myriadrf/Novena-RF/hardware/v1/VIA_OFF_PAD_v.1_r.10/KiCAD/Clocks, RF FE.sch

## KiCad design hardware/v1/VIA_OFF_PAD_v.1_r.10/KiCAD/Clocks, RF FE.sch (2014-10-09)

Schematic: Clocks, RF FE.sch

Parts:
C12, C28, C30, C32, C74, C75, C76, C84, C85: 100nF; C_SM0402; Manufacturer Part Number C0402C104K8PACTU
C26, C77: 100pF; C_SM0402; Manufacturer Part Number GRM1555C1H101JD01D
C29: 1nF; C_SM0402; Manufacturer Part Number CC0402KRX7R9BB102
DA4: CDCV304PW; TSSOP-8; Manufacturer Part Number CDCV304PWR
DA5: PE42440; QFN-16; Manufacturer Part Number PE42440
DA6: PE42422; QFN12; Manufacturer Part Number PE42422MLAA-Z
R2, R3, R50: 1M; R_SM0402; Manufacturer Part Number RC0402FR-071ML
R4, R25, R26, R27, R28, R29, R49: 0; R_SM0402; Manufacturer Part Number RC0402JR-070RL
R69: 49.9; R_SM0402; Manufacturer Part Number MC 0.0625W 0402 1% 49R9
RT1: POT; RT_SMD; Manufacturer Part Number 43WR10KLFTR
X6, X7: U.FL; Manufacturer Part Number 0734120110
XO1: RACON_TXCO_NF; SMD_TXCO; Manufacturer Part Number E5280LF
XO2: RTX5032A_30.72MHZ; SMD_RTX5032A; Manufacturer Part Number 509464

Notes on the sheet:
TX TEST
RX TEST
