myriadrf/Novena-RF/hardware/v1/VIA_OFF_PAD_v.1_r.10/KiCAD/Connectors.sch

## KiCad design hardware/v1/VIA_OFF_PAD_v.1_r.10/KiCAD/Connectors.sch (2014-10-09)

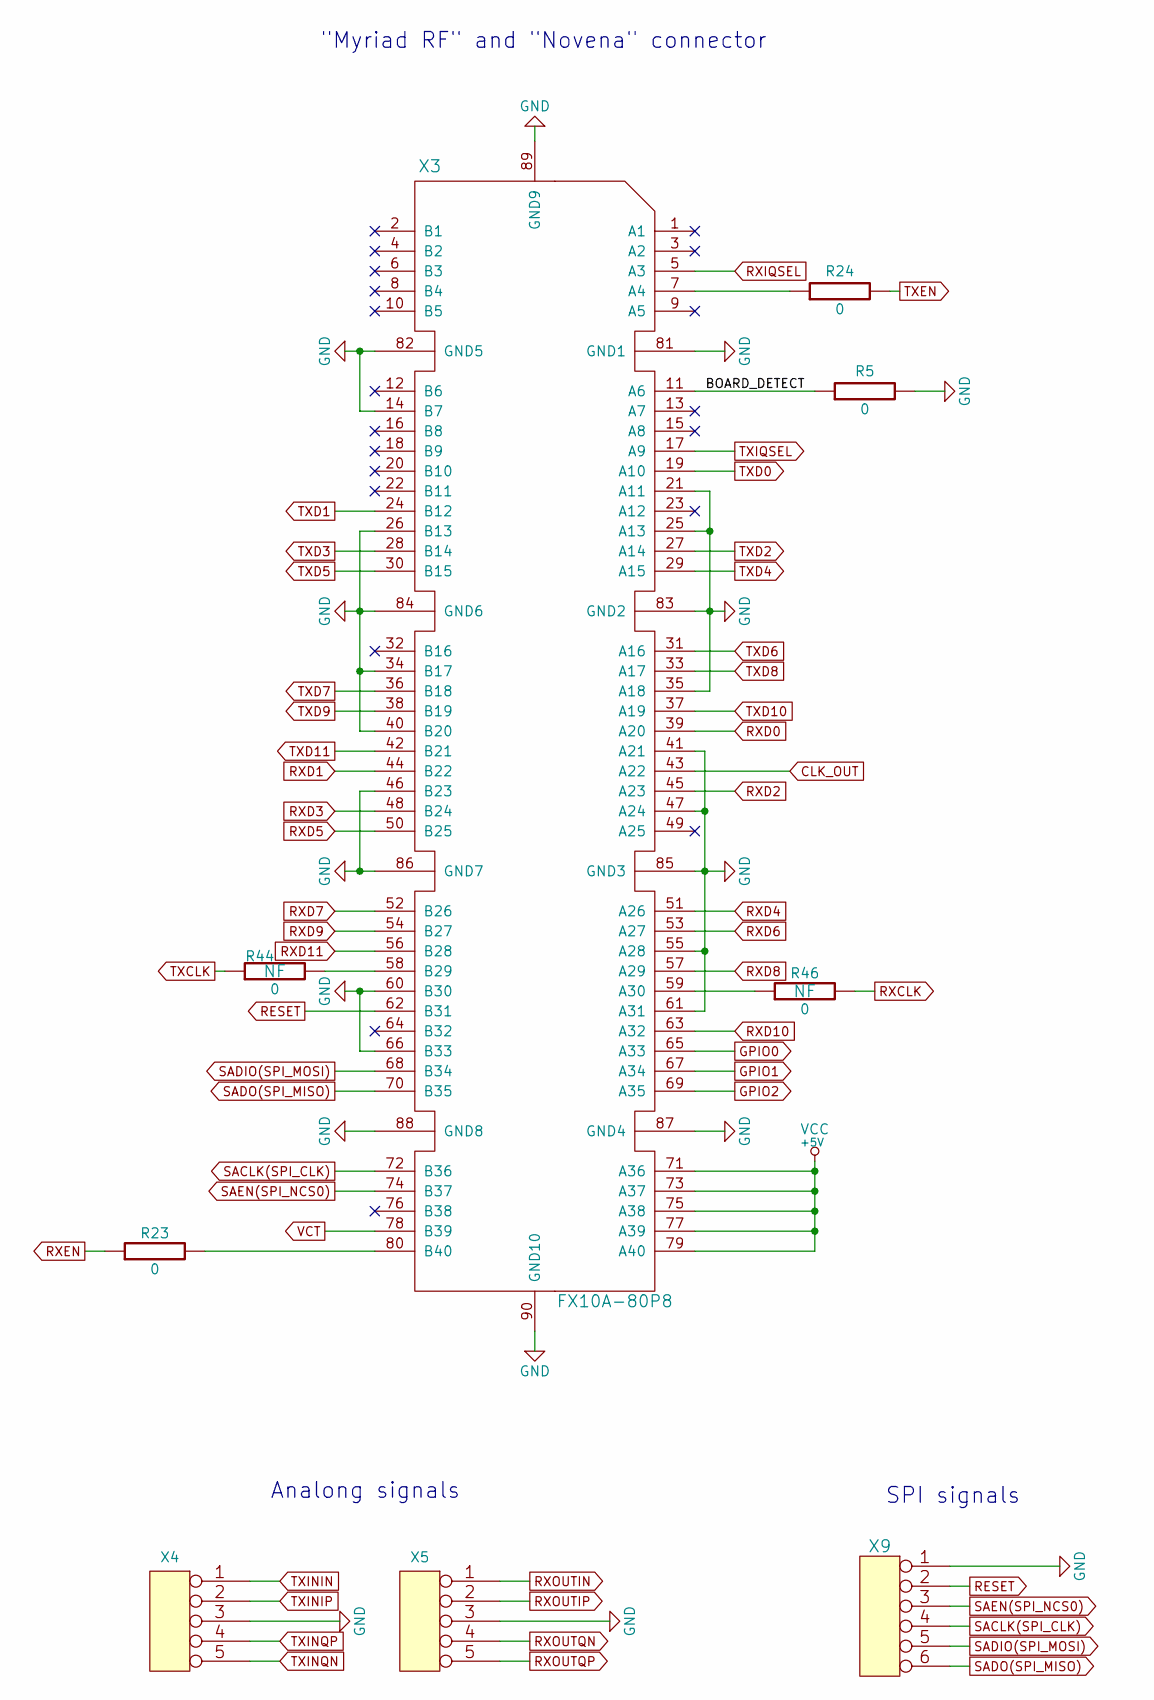
[picture p41: schematic Connectors.sch]

Parts:
R5, R23, R24, R44, R46: 0; R_SM0402; Manufacturer Part Number RC0402JR-070RL
X3: FX10A-80P8; Manufacturer Part Number FX10B-80P/8-SV1(71)
X4, X5: 5-104348-3; VR_pinhead5; Manufacturer Part Number 5-104348-3
X9: CONN_6; pinhead6; Manufacturer Part Number 104345-4

Connections:
BOARD_DETECT: R5.1, X3.11 (A6)
CLK_OUT: X3.43 (A22)
GND: R5.2, X3.14 (B7), X3.21 (A11), X3.25 (A13), X3.26 (B13), X3.34 (B17), X3.35 (A18), X3.40 (B20), X3.41 (A21), X3.46 (B23), X3.47 (A24), X3.55 (A28), X3.60 (B30), X3.61 (A31), X3.66 (B33), X3.81 (GND1), X3.82 (GND5), X3.83 (GND2), X3.84 (GND6), X3.85 (GND3), X3.86 (GND7), X3.87 (GND4), X3.88 (GND8), X3.89 (GND9), X3.90 (GND10), X4.3, X5.3, X9.1
GPIO0: X3.65 (A33)
GPIO1: X3.67 (A34)
GPIO2: X3.69 (A35)
unnamed: R23.2, X3.80 (B40)
unnamed: R24.1, X3.7 (A4)
unnamed: R44.2, X3.58 (B29)
unnamed: R46.1, X3.59 (A30)
RESET: X3.62 (B31), X9.2
RXCLK: R46.2
RXD0: X3.39 (A20)
RXD1: X3.44 (B22)
RXD2: X3.45 (A23)
RXD3: X3.48 (B24)
RXD4: X3.51 (A26)
RXD5: X3.50 (B25)
RXD6: X3.53 (A27)
RXD7: X3.52 (B26)
RXD8: X3.57 (A29)
RXD9: X3.54 (B27)
RXD10: X3.63 (A32)
RXD11: X3.56 (B28)
RXEN: R23.1
RXIQSEL: X3.5 (A3)
RXOUTIN: X5.1
RXOUTIP: X5.2
RXOUTQN: X5.4
RXOUTQP: X5.5
SACLK(SPI_CLK): X3.72 (B36), X9.4
SADIO(SPI_MOSI): X3.68 (B34), X9.5
SADO(SPI_MISO): X3.70 (B35), X9.6
SAEN(SPI_NCS0): X3.74 (B37), X9.3
TXCLK: R44.1
TXD0: X3.19 (A10)
TXD1: X3.24 (B12)
TXD2: X3.27 (A14)
TXD3: X3.28 (B14)
TXD4: X3.29 (A15)
TXD5: X3.30 (B15)
TXD6: X3.31 (A16)
TXD7: X3.36 (B18)
TXD8: X3.33 (A17)
TXD9: X3.38 (B19)
TXD10: X3.37 (A19)
TXD11: X3.42 (B21)
TXEN: R24.2
TXININ: X4.1
TXINIP: X4.2
TXINQN: X4.5
TXINQP: X4.4
TXIQSEL: X3.17 (A9)
VCC: X3.71 (A36), X3.73 (A37), X3.75 (A38), X3.77 (A39), X3.79 (A40)
VCT: X3.78 (B39)

Notes on the sheet:
"Myriad RF" and "Novena" connector
Analong signals
SPI signals
