myriadrf/Novena-RF/hardware/v1/VIA_OFF_PAD_v.1_r.10/KiCAD/Digital Circuits.sch

## KiCad design hardware/v1/VIA_OFF_PAD_v.1_r.10/KiCAD/Digital Circuits.sch (2014-10-09)

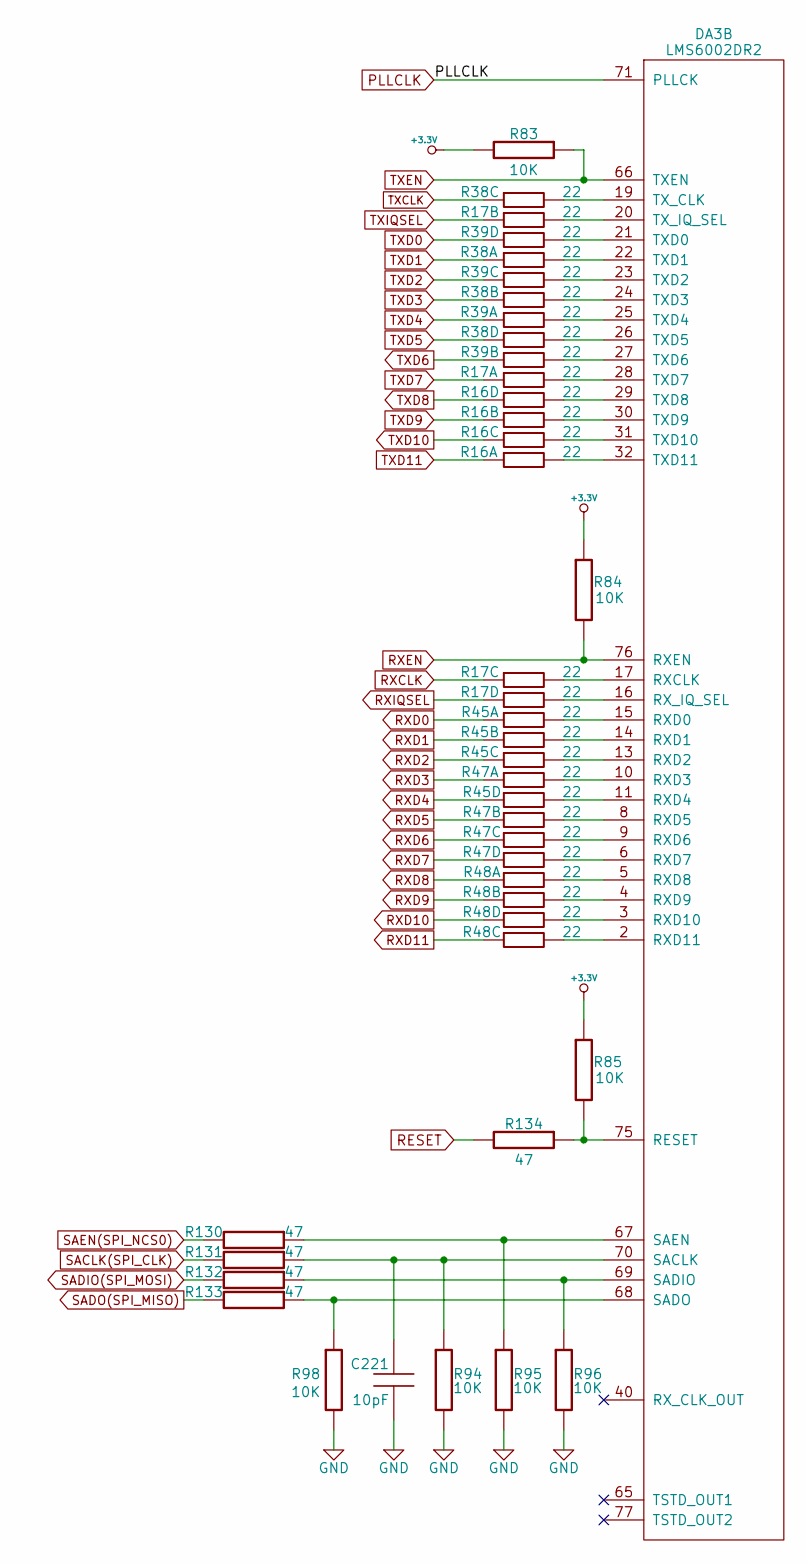
[picture p42: schematic Digital Circuits.sch]

Parts:
C221: 10pF; C_SM0402; Manufacturer Part Number MC0402N100F500CT
DA3: LMS6002DR2; LMS6002; Manufacturer Part Number LMS6002DR2
R16, R17, R38, R39, R45, R47, R48: 22
R83, R84, R85, R94, R95, R96, R98: 10K; R_SM0402; Manufacturer Part Number RC0402FR-1310KL
R130, R131, R132, R133, R134: 47; R_SM0402; Manufacturer Part Number RC0402FR-0747RL

Connections:
+3.3V: R83.2, R84.1, R85.1
GND: C221.2, R94.2, R95.2, R96.2, R98.2
unnamed: C221.1, DA3.70 (SACLK), R94.1, R131.1
unnamed: DA3.2 (RXD11), R48.6
unnamed: DA3.3 (RXD10), R48.5
unnamed: DA3.4 (RXD9), R48.7
unnamed: DA3.5 (RXD8), R48.8
unnamed: DA3.6 (RXD7), R47.5
unnamed: DA3.8 (RXD5), R47.7
unnamed: DA3.9 (RXD6), R47.6
unnamed: DA3.10 (RXD3), R47.8
unnamed: DA3.11 (RXD4), R45.5
unnamed: DA3.13 (RXD2), R45.6
unnamed: DA3.14 (RXD1), R45.7
unnamed: DA3.15 (RXD0), R45.8
unnamed: DA3.16 (RX_IQ_SEL), R17.5
unnamed: DA3.17 (RXCLK), R17.6
unnamed: DA3.19 (TX_CLK), R38.6
unnamed: DA3.20 (TX_IQ_SEL), R17.7
unnamed: DA3.21 (TXD0), R39.5
unnamed: DA3.22 (TXD1), R38.8
unnamed: DA3.23 (TXD2), R39.6
unnamed: DA3.24 (TXD3), R38.7
unnamed: DA3.25 (TXD4), R39.8
unnamed: DA3.26 (TXD5), R38.5
unnamed: DA3.27 (TXD6), R39.7
unnamed: DA3.28 (TXD7), R17.8
unnamed: DA3.29 (TXD8), R16.5
unnamed: DA3.30 (TXD9), R16.7
unnamed: DA3.31 (TXD10), R16.6
unnamed: DA3.32 (TXD11), R16.8
unnamed: DA3.67 (SAEN), R95.1, R130.1
unnamed: DA3.68 (SADO), R98.1, R133.1
unnamed: DA3.69 (SADIO), R96.1, R132.1
unnamed: DA3.75 (RESET), R85.2, R134.1
PLLCLK: DA3.71 (PLLCK)
RESET: R134.2
RXCLK: R17.3
RXD0: R45.1
RXD1: R45.2
RXD2: R45.3
RXD3: R47.1
RXD4: R45.4
RXD5: R47.2
RXD6: R47.3
RXD7: R47.4
RXD8: R48.1
RXD9: R48.2
RXD10: R48.4
RXD11: R48.3
RXEN: DA3.76 (RXEN), R84.2
RXIQSEL: R17.4
SACLK(SPI_CLK): R131.2
SADIO(SPI_MOSI): R132.2
SADO(SPI_MISO): R133.2
SAEN(SPI_NCS0): R130.2
TXCLK: R38.3
TXD0: R39.4
TXD1: R38.1
TXD2: R39.3
TXD3: R38.2
TXD4: R39.1
TXD5: R38.4
TXD6: R39.2
TXD7: R17.1
TXD8: R16.4
TXD9: R16.2
TXD10: R16.3
TXD11: R16.1
TXEN: DA3.66 (TXEN), R83.1
TXIQSEL: R17.2
