myriadrf/Novena-RF/driver/fpga/bclk_dll/bclk_dll.vhd

-- file: bclk_dll.vhd
-- 
-- (c) Copyright 2008 - 2011 Xilinx, Inc. All rights reserved.
-- 
-- This file contains confidential and proprietary information
-- of Xilinx, Inc. and is protected under U.S. and
-- international copyright and other intellectual property
-- laws.
-- 
-- DISCLAIMER
-- This disclaimer is not a license and does not grant any
-- rights to the materials distributed herewith. Except as
-- otherwise provided in a valid license issued to you by
-- Xilinx, and to the maximum extent permitted by applicable
-- law: (1) THESE MATERIALS ARE MADE AVAILABLE "AS IS" AND
-- WITH ALL FAULTS, AND XILINX HEREBY DISCLAIMS ALL WARRANTIES
-- AND CONDITIONS, EXPRESS, IMPLIED, OR STATUTORY, INCLUDING
-- BUT NOT LIMITED TO WARRANTIES OF MERCHANTABILITY, NON-
-- INFRINGEMENT, OR FITNESS FOR ANY PARTICULAR PURPOSE; and
-- (2) Xilinx shall not be liable (whether in contract or tort,
-- including negligence, or under any other theory of
-- liability) for any loss or damage of any kind or nature
-- related to, arising under or in connection with these
-- materials, including for any direct, or any indirect,
-- special, incidental, or consequential loss or damage
-- (including loss of data, profits, goodwill, or any type of
-- loss or damage suffered as a result of any action brought
-- by a third party) even if such damage or loss was
-- reasonably foreseeable or Xilinx had been advised of the
-- possibility of the same.
-- 
-- CRITICAL APPLICATIONS
-- Xilinx products are not designed or intended to be fail-
-- safe, or for use in any application requiring fail-safe
-- performance, such as life-support or safety devices or
-- systems, Class III medical devices, nuclear facilities,
-- applications related to the deployment of airbags, or any
-- other applications that could lead to death, personal
-- injury, or severe property or environmental damage
-- (individually and collectively, "Critical
-- Applications"). Customer assumes the sole risk and
-- liability of any use of Xilinx products in Critical
-- Applications, subject only to applicable laws and
-- regulations governing limitations on product liability.
-- 
-- THIS COPYRIGHT NOTICE AND DISCLAIMER MUST BE RETAINED AS
-- PART OF THIS FILE AT ALL TIMES.
-- 
------------------------------------------------------------------------------
-- User entered comments
------------------------------------------------------------------------------
-- None
--
------------------------------------------------------------------------------
-- "Output    Output      Phase     Duty      Pk-to-Pk        Phase"
-- "Clock    Freq (MHz) (degrees) Cycle (%) Jitter (ps)  Error (ps)"
------------------------------------------------------------------------------
-- CLK_OUT1___133.014______0.000______50.0______200.000____150.000
--
------------------------------------------------------------------------------
-- "Input Clock   Freq (MHz)    Input Jitter (UI)"
------------------------------------------------------------------------------
-- __primary_________133.014_____________0.01

library ieee;
use ieee.std_logic_1164.all;
use ieee.std_logic_unsigned.all;
use ieee.std_logic_arith.all;
use ieee.numeric_std.all;

library unisim;
use unisim.vcomponents.all;

entity bclk_dll is
port
 (-- Clock in ports
  clk133in           : in     std_logic;
  -- Clock out ports
  clk133          : out    std_logic;
  -- Status and control signals
  RESET             : in     std_logic;
  LOCKED            : out    std_logic
 );
end bclk_dll;

architecture xilinx of bclk_dll is
  attribute CORE_GENERATION_INFO : string;
  attribute CORE_GENERATION_INFO of xilinx : architecture is "bclk_dll,clk_wiz_v4_1,{component_name=bclk_dll,use_phase_alignment=true,use_min_o_jitter=false,use_max_i_jitter=false,use_dyn_phase_shift=false,use_inclk_switchover=false,use_dyn_reconfig=false,feedback_source=FDBK_AUTO,primtype_sel=DCM_SP,num_out_clk=1,clkin1_period=7.518,clkin2_period=7.518,use_power_down=false,use_reset=true,use_locked=true,use_inclk_stopped=false,use_status=false,use_freeze=false,use_clk_valid=false,feedback_type=SINGLE,clock_mgr_type=AUTO,manual_override=false}";
	  -- Input clock buffering / unused connectors
  signal clkin1            : std_logic;
  -- Output clock buffering
  signal clk_out1_internal : std_logic;
  signal clkfb             : std_logic;
  signal clk0              : std_logic;
  signal clkfbout          : std_logic;
  signal locked_internal   : std_logic;
  signal status_internal   : std_logic_vector(7 downto 0);
begin


  -- Input buffering
  --------------------------------------
  clkin1 <= clk133in;


  -- Clocking primitive
  --------------------------------------
  
  -- Instantiation of the DCM primitive
  --    * Unused inputs are tied off
  --    * Unused outputs are labeled unused
  dcm_sp_inst: DCM_SP
  generic map
   (CLKDV_DIVIDE          => 2.000,
    CLKFX_DIVIDE          => 1,
    CLKFX_MULTIPLY        => 4,
    CLKIN_DIVIDE_BY_2     => FALSE,
    CLKIN_PERIOD          => 7.518,
    CLKOUT_PHASE_SHIFT    => "NONE",
    CLK_FEEDBACK          => "1X",
    DESKEW_ADJUST         => "SYSTEM_SYNCHRONOUS",
    PHASE_SHIFT           => 0,
    STARTUP_WAIT          => FALSE)
  port map
   -- Input clock
   (CLKIN                 => clkin1,
    CLKFB                 => clkfb,
    -- Output clocks
    CLK0                  => clk0,
    CLK90                 => open,
    CLK180                => open,
    CLK270                => open,
    CLK2X                 => open,
    CLK2X180              => open,
    CLKFX                 => open,
    CLKFX180              => open,
    CLKDV                 => open,
   -- Ports for dynamic phase shift
    PSCLK                 => '0',
    PSEN                  => '0',
    PSINCDEC              => '0',
    PSDONE                => open,
   -- Other control and status signals
    LOCKED                => locked_internal,
    STATUS                => status_internal,
    RST                   => RESET,
   -- Unused pin, tie low
    DSSEN                 => '0');

  LOCKED                <= locked_internal;



  -- Output buffering
  -------------------------------------
  clkfb <= clk_out1_internal;


  clkout1_buf : BUFG
  port map
   (O   => clk_out1_internal,
    I   => clk0);


  clk133 <= clk_out1_internal;

end xilinx;
