myriadrf/Novena-RF/driver/host/NovenaLMS6.cpp

////////////////////////////////////////////////////////////////////////
// SoapySDR module for Novena-RF SDR
//
// Copyright (c) 2015-2015 Lime Microsystems
// Copyright (c) 2015-2015 Andrew "bunnie" Huang
// SPDX-License-Identifier: Apache-2.0
// http://www.apache.org/licenses/LICENSE-2.0
////////////////////////////////////////////////////////////////////////

#include "NovenaRF.hpp"
#include "LMS6002_MainControl.h"
#include "lms6/CompoundOperations.h"
#include "lms6/Algorithms.h"
#include "MessageLog.h"

#include <sys/stat.h>
#include <pthread.h>
#include <fstream>

/***********************************************************************
 * Log handler from the lms suite
 **********************************************************************/
class SignalHandlerLogger : public SignalHandler
{
public:
    SignalHandlerLogger(void)
    {
        return;
    }

    void HandleMessage(const LMS_Message &msg)
    {
        switch (msg.type)
        {
        case MSG_ERROR: SoapySDR::log(SOAPY_SDR_ERROR, msg.text); break;
        case MSG_WARNING: SoapySDR::log(SOAPY_SDR_WARNING, msg.text); break;
        default: SoapySDR::log(SOAPY_SDR_INFO, msg.text); break;
        }
    }
};

static SignalHandlerLogger myLogger;

/***********************************************************************
 * handler for interfacing with LMS6 registers from unix fifo
 **********************************************************************/
#define NOVENA_RF_CMD_PATH "/tmp/novena_rf_cmd"
#define NOVENA_RF_OUT_PATH "/tmp/novena_rf_out"
static pthread_t fifoAccessThread;

void *fifoAccessHandler(void *arg)
{
    auto regMap = reinterpret_cast<lms6::RegistersMap *>(arg);

    mkfifo(NOVENA_RF_CMD_PATH, S_IWUSR | S_IRUSR);
    mkfifo(NOVENA_RF_OUT_PATH, S_IWUSR | S_IRUSR);

    while (true)
    {
        //read cmd fifo
        std::ifstream cmdFile(NOVENA_RF_CMD_PATH);
        std::string line;
        std::getline(cmdFile, line);
        if (line.empty()) continue;
        if (line == "exit") break;

        //parse command
        std::string adrStr, valStr;
        std::stringstream ss(line);
        std::getline(ss, adrStr, ' ');
        std::getline(ss, valStr, ' ');
        const long adr = (adrStr.substr(0, 2) == "0x")?strtol(adrStr.c_str(), nullptr, 16):strtol(adrStr.c_str(), nullptr, 10);
        const long val = (valStr.substr(0, 2) == "0x")?strtol(valStr.c_str(), nullptr, 16):strtol(valStr.c_str(), nullptr, 10);

        //perform write it value specified
        if (not valStr.empty()) regMap->SetRegisterValue(adr, val);

        //perform a read and output to the result
        const int out = regMap->GetRegisterValue(adr, true/*from chip*/);
        std::ofstream outFile(NOVENA_RF_OUT_PATH);
        outFile << std::hex << "0x" << out << std::endl;
    }

    return nullptr;
}

/***********************************************************************
 * Setup and tear-down hooks
 * Initialize everything on the lms6 for runtime usage.
 * Configurable parameters are in the sections below.
 **********************************************************************/
void NovenaRF::initRFIC(void)
{
    _calLPFCoreOnce = 0;

    auto ser = new ConnectionManager();
    ser->RegisterForNotifications(&myLogger);
    ser->Open();

    //separate logger - enable to console
    //MessageLog::getInstance()->SetConsoleFilter(LOG_ALL, true);

    //main control owns the connection manager
    _lms6ctrl = new lms6::LMS6002_MainControl(ser);
    _lms6ctrl->ResetChip(LMS_RST_PULSE);
    _lms6ctrl->NewProject();
    SoapySDR::logf(SOAPY_SDR_INFO, "LMS6002: ver=0x%x, rev=0x%x",
        _lms6ctrl->GetParam(lms6::VER), _lms6ctrl->GetParam(lms6::REV));

    _lms6ctrl->SetReferenceFrequency(this->getMasterClockRate()/1e6, true/*Rx*/);
    _lms6ctrl->SetReferenceFrequency(this->getMasterClockRate()/1e6, false/*Tx*/);

    _lms6ctrl->SetParam(lms6::STXEN, 1); //enable transmitter
    _lms6ctrl->SetParam(lms6::SRXEN, 1); //enable receiver

    //enable all the things
    _lms6ctrl->SetParam(lms6::EN_TOP, 1);
    _lms6ctrl->SetParam(lms6::EN_RXPLL, 1);
    _lms6ctrl->SetParam(lms6::EN_TXPLL, 1);
    _lms6ctrl->SetParam(lms6::EN_ADC_DAC, 1);
    _lms6ctrl->SetParam(lms6::EN_TXRF, 1);
    _lms6ctrl->SetParam(lms6::EN_RXFE, 1);
    _lms6ctrl->SetParam(lms6::EN_RXLPF, 1);
    _lms6ctrl->SetParam(lms6::EN_TXLPF, 1);
    _lms6ctrl->SetParam(lms6::EN_RXVGA2, 1);
    lms6::CompoundOperations(_lms6ctrl).CustSet_RxVGA2PowerON();
    lms6::CompoundOperations(_lms6ctrl).CustSet_LNAPowerON();
    lms6::CompoundOperations(_lms6ctrl).CustSet_RxLpfPowerON();
    lms6::CompoundOperations(_lms6ctrl).CustSet_RxFePowerON();

    //bypass LPF by default with large BW
    this->setBandwidth(SOAPY_SDR_TX, 0, 30.0e6);
    this->setBandwidth(SOAPY_SDR_RX, 0, 30.0e6);

    //initialize to minimal gain settings
    SoapySDR::Device::setGain(SOAPY_SDR_TX, 0, 0.0);
    SoapySDR::Device::setGain(SOAPY_SDR_RX, 0, 0.0);

    //initialize antenna to broadband
    this->setAntenna(SOAPY_SDR_TX, 0, "BB");
    this->setAntenna(SOAPY_SDR_RX, 0, "BB");

    //set expected interface mode
    _lms6ctrl->SetParam(lms6::MISC_CTRL_9, 0); //rx fsync polarity
    _lms6ctrl->SetParam(lms6::MISC_CTRL_8, 1); //rx interleave mode (swap for std::complex host format)
    _lms6ctrl->SetParam(lms6::MISC_CTRL_6, 1); //tx fsync polarity (tx needs this swap for an unknown reason)
    _lms6ctrl->SetParam(lms6::MISC_CTRL_5, 1); //tx interleave mode (swap for std::complex host format)

    //start the register handler thread
    if (pthread_create(&fifoAccessThread, nullptr, fifoAccessHandler, _lms6ctrl->getRegistersMap()) != 0)
    {
        SoapySDR::log(SOAPY_SDR_ERROR, "Error creating fifo access thread");
    }
}

void NovenaRF::exitRFIC(void)
{
    //stop the register handler thread
    std::ofstream cmdFile(NOVENA_RF_CMD_PATH);
    cmdFile << "exit" << std::endl;
    cmdFile.close();
    pthread_join(fifoAccessThread, nullptr);

    //_lms6ctrl->SaveToFile("/tmp/lms6.txt", false);
    _lms6ctrl->SetParam(lms6::STXEN, 0); //disable transmitter
    _lms6ctrl->SetParam(lms6::SRXEN, 0); //disable receiver
    lms6::CompoundOperations(_lms6ctrl).CustSet_RxVGA2PowerOFF();
    lms6::CompoundOperations(_lms6ctrl).CustSet_LNAPowerOFF();
    lms6::CompoundOperations(_lms6ctrl).CustSet_RxLpfPowerOFF();
    lms6::CompoundOperations(_lms6ctrl).CustSet_RxFePowerOFF();

    delete _lms6ctrl;
    _lms6ctrl = nullptr;
}

/*******************************************************************
 * Gain API
 *
 * Available amplification/attenuation elements are listed in order
 * from RF to BB for the default gain distribution algorithm.
 *
 * Gains are passed in as dB and clipped and scaled into integer values
 * for the specific registers to which they apply.
 ******************************************************************/
std::vector<std::string> NovenaRF::listGains(const int direction, const size_t channel) const
{
    std::vector<std::string> gains;
    if (direction == SOAPY_SDR_TX)
    {
        //ordering RF to BB
        gains.push_back("VGA2");
        gains.push_back("VGA1");
    }
    if (direction == SOAPY_SDR_RX)
    {
        //ordering RF to BB
        gains.push_back("LNA");
        gains.push_back("VGA1");
        gains.push_back("VGA2");
    }
    return gains;
}

#define MinMaxClip(minimum, maximum, value) \
    std::max(minimum, std::min(maximum, value))

void NovenaRF::setGain(const int direction, const size_t channel, const std::string &name, const double value)
{
    if (direction == SOAPY_SDR_TX and name == "VGA1")
    {
        const double regVal(MinMaxClip(-35.0, -4.0, value));
        _lms6ctrl->SetParam(lms6::VGA1GAIN, lrint(regVal+35.0));
    }
    if (direction == SOAPY_SDR_TX and name == "VGA2")
    {
        const double regVal(MinMaxClip(0.0, 25.0, value));
        _lms6ctrl->SetParam(lms6::VGA2GAIN_TXVGA2, lrint(regVal));
    }
    if (direction == SOAPY_SDR_RX and name == "VGA2")
    {
        const double regVal(MinMaxClip(0.0, 30.0, value));
        _lms6ctrl->SetParam(lms6::VGA2GAIN_RXVGA2, lrint(regVal/3.0));
    }
    if (direction == SOAPY_SDR_RX and name == "VGA1")
    {
        const double regVal(MinMaxClip(0.0, 30.0, value));
        _lms6ctrl->SetParam(lms6::RFB_TIA_RXFE, regVal*4);
    }
    if (direction == SOAPY_SDR_RX and name == "LNA")
    {
        const double regVal(MinMaxClip(0.0, 6.0, value));
        _lms6ctrl->SetParam(lms6::G_LNA_RXFE, 2 | lrint(regVal/6.0));
    }
}

double NovenaRF::getGain(const int direction, const size_t channel, const std::string &name) const
{
    if (direction == SOAPY_SDR_TX and name == "VGA1")
    {
        return _lms6ctrl->GetParam(lms6::VGA1GAIN) - 35.0;
    }
    if (direction == SOAPY_SDR_TX and name == "VGA2")
    {
        return _lms6ctrl->GetParam(lms6::VGA2GAIN_TXVGA2);
    }
    if (direction == SOAPY_SDR_RX and name == "VGA2")
    {
        return _lms6ctrl->GetParam(lms6::VGA2GAIN_RXVGA2)*3.0;
    }
    if (direction == SOAPY_SDR_RX and name == "VGA1")
    {
        return _lms6ctrl->GetParam(lms6::RFB_TIA_RXFE)/4.0;
    }
    if (direction == SOAPY_SDR_RX and name == "LNA")
    {
        return (_lms6ctrl->GetParam(lms6::G_LNA_RXFE) & 0x1)*6.0;
    }
    return SoapySDR::Device::getGain(direction, channel, name);
}

SoapySDR::Range NovenaRF::getGainRange(const int direction, const size_t channel, const std::string &name) const
{
    if (direction == SOAPY_SDR_TX and name == "VGA1") return SoapySDR::Range(-35.0, -4.0);
    if (direction == SOAPY_SDR_TX and name == "VGA2") return SoapySDR::Range(0.0, 25.0);
    if (direction == SOAPY_SDR_RX and name == "VGA2") return SoapySDR::Range(0.0, 30.0);
    if (direction == SOAPY_SDR_RX and name == "VGA1") return SoapySDR::Range(0.0, 30.0);
    if (direction == SOAPY_SDR_RX and name == "LNA") return SoapySDR::Range(0.0, 6.0);
    return SoapySDR::Device::getGainRange(direction, channel, name);
}

/*******************************************************************
 * Frequency API
 *
 * The LO is tuned to the specified frequency in Hz
 * and then the calibration algorithm is applied.
 * Error in tuning the LO is compensated in the CORDIC
 * through the default tuning algorithm.
 ******************************************************************/
void NovenaRF::setRfFrequency(const int direction, const size_t channel, const double frequency, const SoapySDR::Kwargs &)
{
    double realFreq, fVco;
    unsigned Nint, Nfrac, iVco;
    int divider;

    _lms6ctrl->SetFrequency(direction == SOAPY_SDR_RX, frequency/1e6, realFreq, Nint, Nfrac, iVco, fVco, divider);
    _lms6ctrl->Tune(direction == SOAPY_SDR_RX);
    SoapySDR::logf(SOAPY_SDR_TRACE, "NovenaRF: %sTune(%f MHz), actual = %f MHz", (direction==SOAPY_SDR_TX)?"TX":"RX", frequency/1e6, realFreq);
    //SoapySDR::logf(SOAPY_SDR_TRACE, "fVco=%f, Nint=%d, Nfrac=%d, iVco=%d, divider=%d", fVco, Nint, Nfrac, iVco, divider);

    //save gain values
    std::map<std::string, double> save;
    for (const auto &name : this->listGains(direction, channel))
    {
        save[name] = this->getGain(direction, channel, name);
    }

    //apply gain
    if (direction == SOAPY_SDR_RX)
    {
        auto r = SoapySDR::Device::getGainRange(direction, channel);
        SoapySDR::Device::setGain(direction, channel, r.maximum());
    }
    if (direction == SOAPY_SDR_TX)
    {
        this->setGain(direction, channel, "VGA1", -10);
        this->setGain(direction, channel, "VGA2", 25);
    }

    //perform cal with adc off
    _lms6ctrl->SetParam(lms6::EN_ADC_DAC, 0);
    if (_calLPFCoreOnce++ == 0) lms6::Algorithms(_lms6ctrl).CalibrateLPFCore();
    if (direction == SOAPY_SDR_TX) lms6::Algorithms(_lms6ctrl).CalibrateTx();
    if (direction == SOAPY_SDR_RX) lms6::Algorithms(_lms6ctrl).CalibrateRx();
    _lms6ctrl->SetParam(lms6::EN_ADC_DAC, 1);

    //restore gain values
    for (const auto &pair : save)
    {
        this->setGain(direction, channel, pair.first, pair.second);
    }
}

void NovenaRF::setFrequency(const int direction, const size_t channel, const std::string &name, const double frequency, const SoapySDR::Kwargs &args)
{
    //printf("setFrequency %s %f MHz\n", name.c_str(), frequency/1e6);
    if (name == "RF")
    {
        return this->setRfFrequency(direction, channel, frequency, args);
    }
    if (name == "BB")
    {
        //set the cordic rate
        const double cordicFreq = frequency;
        const double dspRate = LMS_CLOCK_RATE/2;
        uint32_t cordicWord = int32_t(cordicFreq*(1 << 31)/dspRate);
        uint32_t scaledWord = -2*int32_t(cordicWord);
        if (direction == SOAPY_SDR_RX)
        {
            this->writeRegister(REG_DECIM_CORDIC_PHASE_LO, scaledWord & 0xffff);
            this->writeRegister(REG_DECIM_CORDIC_PHASE_HI, scaledWord >> 16);
        }
        if (direction == SOAPY_SDR_TX)
        {
            this->writeRegister(REG_INTERP_CORDIC_PHASE_LO, scaledWord & 0xffff);
            this->writeRegister(REG_INTERP_CORDIC_PHASE_HI, scaledWord >> 16);
        }
        _cachedCordics[direction][channel] = (cordicWord*dspRate)/double(1 << 31);
        return;
    }
    return SoapySDR::Device::setFrequency(direction, channel, name, frequency);
}

double NovenaRF::getFrequency(const int direction, const size_t channel, const std::string &name) const
{
    if (name == "RF")
    {
        return _lms6ctrl->GetFrequency(direction == SOAPY_SDR_RX)*1e6;
    }
    if (name == "BB")
    {
        return _cachedCordics.at(direction).at(channel);
    }
    return SoapySDR::Device::getFrequency(direction, channel, name);
}

SoapySDR::RangeList NovenaRF::getFrequencyRange(const int direction, const size_t channel, const std::string &name) const
{
    if (name == "RF")
    {
        return SoapySDR::RangeList(1, SoapySDR::Range(0.3e9, 3.8e9));
    }
    if (name == "BB")
    {
        const double dspRate = LMS_CLOCK_RATE/2;
        return SoapySDR::RangeList(1, SoapySDR::Range(-dspRate/2, dspRate/2));
    }
    return SoapySDR::Device::getFrequencyRange(direction, channel, name);
}

std::vector<std::string> NovenaRF::listFrequencies(const int direction, const size_t channel) const
{
    //order RF to BB for default tuning algorithm
    std::vector<std::string> comps;
    comps.push_back("RF");
    comps.push_back("BB");
    return comps;
}

/*******************************************************************
 * Bandwidth filters API
 ******************************************************************/
void NovenaRF::setBandwidth(const int direction, const size_t channel, const double bw)
{
    //map the requested frequency to the next greatest bandwidth setting
    const auto bws = this->listBandwidths(direction, channel);
    long val = 0;
    while (val < 0xf)
    {
        if (bw >= bws.at(val)) break;
        val++;
    }

    //bypass when BW is larger than max filter
    const bool bypass = (bw/2.0 > 14e6);
    if (direction == SOAPY_SDR_TX and bypass)     lms6::CompoundOperations(_lms6ctrl).CustSet_BypassTxLpfON();
    if (direction == SOAPY_SDR_TX and not bypass) lms6::CompoundOperations(_lms6ctrl).CustSet_BypassTxLpfOFF();
    if (direction == SOAPY_SDR_RX and bypass)     lms6::CompoundOperations(_lms6ctrl).CustSet_BypassRxLpfON();
    if (direction == SOAPY_SDR_RX and not bypass) lms6::CompoundOperations(_lms6ctrl).CustSet_BypassRxLpfOFF();

    //write the setting
    const auto reg = (direction == SOAPY_SDR_RX)?lms6::BWC_LPF_RXLPF:lms6::BWC_LPF_TXLPF;
    _lms6ctrl->SetParam(reg, val);
}

double NovenaRF::getBandwidth(const int direction, const size_t channel) const
{
    const auto reg = (direction == SOAPY_SDR_RX)?lms6::BWC_LPF_RXLPF:lms6::BWC_LPF_TXLPF;
    long val = _lms6ctrl->GetParam(reg);
    return this->listBandwidths(direction, channel).at(val & 0xf);
}

std::vector<double> NovenaRF::listBandwidths(const int direction, const size_t channel) const
{
    std::vector<double> bws;
    bws.push_back(14e6);
    bws.push_back(10e6);
    bws.push_back(7e6);
    bws.push_back(6e6);
    bws.push_back(5e6);
    bws.push_back(4.375e6);
    bws.push_back(3.5e6);
    bws.push_back(3e6);
    bws.push_back(2.75e6);
    bws.push_back(2.5e6);
    bws.push_back(1.92e6);
    bws.push_back(1.5e6);
    bws.push_back(1.375e6);
    bws.push_back(1.25e6);
    bws.push_back(0.875e6);
    bws.push_back(0.75e6);
    for (auto &bw : bws) bw *= 2; //convert to complex width in Hz
    return bws;
}

/*******************************************************************
 * Antenna API
 ******************************************************************/
std::vector<std::string> NovenaRF::listAntennas(const int direction, const size_t channel) const
{
    std::vector<std::string> ants;
    if (direction == SOAPY_SDR_TX)
    {
        //1: High band output (1500 - 3800 MHz)
        //2: Broadband output
        ants.push_back("HB");
        ants.push_back("BB");
    }
    if (direction == SOAPY_SDR_RX)
    {
        //1: Low band input (300 - 2200 MHz)
        //2: High band input (1500-3800MHz)
        //3: Broadband input
        ants.push_back("LB");
        ants.push_back("HB");
        ants.push_back("BB");
    }
    return ants;
}

void NovenaRF::setAntenna(const int direction, const size_t channel, const std::string &name)
{
    if (direction == SOAPY_SDR_TX)
    {
        if (name == "HB") _lms6ctrl->SetParam(lms6::PA_EN, 1);
        else              _lms6ctrl->SetParam(lms6::PA_EN, 2);
    }
    else
    {
        if      (name == "LB") _lms6ctrl->SetParam(lms6::LNASEL_RXFE, 1);
        else if (name == "HB") _lms6ctrl->SetParam(lms6::LNASEL_RXFE, 2);
        else                   _lms6ctrl->SetParam(lms6::LNASEL_RXFE, 3);
    }
}

std::string NovenaRF::getAntenna(const int direction, const size_t channel) const
{
    if (direction == SOAPY_SDR_TX)
    {
        switch (_lms6ctrl->GetParam(lms6::PA_EN))
        {
        case 1: return "HB";
        default: return "BB";
        }
    }
    if (direction == SOAPY_SDR_RX)
    {
        switch (_lms6ctrl->GetParam(lms6::LNASEL_RXFE))
        {
        case 1: return "LB";
        case 2: return "HB";
        default: return "BB";
        }
    }
    return SoapySDR::Device::getAntenna(direction, channel);
}
